m-stefanski/skunk/src/skunk.svg.h

0x3c, 0x73, 0x76, 0x67, 0x20, 0x69, 0x64, 0x3d, 0x22, 0x65, 0x6d, 0x6f, 0x6a, 0x69, 0x22, 0x20, 0x76, 0x69, 0x65, 0x77, 0x42, 0x6f, 0x78, 0x3d, 0x22, 0x30, 0x20, 0x30, 0x20, 0x37, 0x32, 0x20, 0x37, 0x32, 0x22, 0x20, 0x78, 0x6d, 0x6c, 0x6e, 0x73, 0x3d, 0x22, 0x68, 0x74, 0x74, 0x70, 0x3a, 0x2f, 0x2f, 0x77, 0x77, 0x77, 0x2e, 0x77, 0x33, 0x2e, 0x6f, 0x72, 0x67, 0x2f, 0x32, 0x30, 0x30, 0x30, 0x2f, 0x73, 0x76, 0x67, 0x22, 0x3e, 0x0a, 0x20, 0x20, 0x3c, 0x67, 0x20, 0x69, 0x64, 0x3d, 0x22, 0x63, 0x6f, 0x6c, 0x6f, 0x72, 0x22, 0x3e, 0x0a, 0x20, 0x20, 0x20, 0x20, 0x3c, 0x70, 0x61, 0x74, 0x68, 0x20, 0x66, 0x69, 0x6c, 0x6c, 0x3d, 0x22, 0x23, 0x33, 0x66, 0x33, 0x66, 0x33, 0x66, 0x22, 0x20, 0x64, 0x3d, 0x22, 0x4d, 0x32, 0x39, 0x2e, 0x33, 0x36, 0x38, 0x39, 0x2c, 0x35, 0x34, 0x2e, 0x33, 0x39, 0x36, 0x36, 0x6c, 0x2d, 0x31, 0x2e, 0x31, 0x2c, 0x33, 0x2d, 0x33, 0x2c, 0x33, 0x2e, 0x31, 0x68, 0x2d, 0x34, 0x63, 0x2d, 0x31, 0x2e, 0x36, 0x2d, 0x31, 0x2e, 0x32, 0x2c, 0x33, 0x2e, 0x34, 0x2d, 0x33, 0x2e, 0x37, 0x2c, 0x33, 0x2e, 0x34, 0x2d, 0x33, 0x2e, 0x37, 0x76, 0x2d, 0x33, 0x2e, 0x37, 0x6c, 0x2d, 0x2e, 0x32, 0x2d, 0x33, 0x2e, 0x31, 0x41, 0x31, 0x35, 0x2e, 0x38, 0x35, 0x37, 0x34, 0x2c, 0x31, 0x35, 0x2e, 0x38, 0x35, 0x37, 0x34, 0x2c, 0x30, 0x2c, 0x30, 0x2c, 0x31, 0x2c, 0x32, 0x39, 0x2e, 0x33, 0x36, 0x38, 0x39, 0x2c, 0x35, 0x34, 0x2e, 0x33, 0x39, 0x36, 0x36, 0x5a, 0x22, 0x2f, 0x3e, 0x0a, 0x20, 0x20, 0x20, 0x20, 0x3c, 0x70, 0x61, 0x74, 0x68, 0x20, 0x66, 0x69, 0x6c, 0x6c, 0x3d, 0x22, 0x23, 0x33, 0x66, 0x33, 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
