m-stefanski/skunk/src/favicon.png.h

0x89, 0x50, 0x4e, 0x47, 0x0d, 0x0a, 0x1a, 0x0a, 0x00, 0x00, 0x00, 0x0d, 0x49, 0x48, 0x44, 0x52, 0x00, 0x00, 0x00, 0xb4, 0x00, 0x00, 0x00, 0xb4, 0x04, 0x00, 0x00, 0x00, 0x00, 0xdd, 0x56, 0xb4, 0xef, 0x00, 0x00, 0x00, 0x09, 0x70, 0x48, 0x59, 0x73, 0x00, 0x00, 0x24, 0xe8, 0x00, 0x00, 0x24, 0xe8, 0x01, 0x82, 0x63, 0x05, 0x1c, 0x00, 0x00, 0x00, 0x19, 0x74, 0x45, 0x58, 0x74, 0x53, 0x6f, 0x66, 0x74, 0x77, 0x61, 0x72, 0x65, 0x00, 0x77, 0x77, 0x77, 0x2e, 0x69, 0x6e, 0x6b, 0x73, 0x63, 0x61, 0x70, 0x65, 0x2e, 0x6f, 0x72, 0x67, 0x9b, 0xee, 0x3c, 0x1a, 0x00, 0x00, 0x08, 0x27, 0x49, 0x44, 0x41, 0x54, 0x68, 0xde, 0xed, 0x9a, 0x5b, 0x6c, 0x14, 0x65, 0x14, 0x80, 0xcf, 0xee, 0xd2, 0x52, 0x2e, 0xea, 0x42, 0xf1, 0xde, 0xc4, 0x61, 0x57, 0xe5, 0x41, 0x12, 0xa7, 0x9d, 0xa5, 0x08, 0xa2, 0xa2, 0xab, 0x88, 0x8a, 0x72, 0x13, 0x12, 0xb4, 0xda, 0x0a, 0x28, 0xa0, 0x55, 0x49, 0x30, 0x85, 0x60, 0x0d, 0x8d, 0x4a, 0x88, 0xb1, 0x4a, 0x4d, 0x80, 0x44, 0xad, 0x42, 0x42, 0x8c, 0x3e, 0x6c, 0xa0, 0x48, 0xc5, 0x20, 0x9b, 0x60, 0x29, 0xb5, 0xbb, 0x3b, 0x5b, 0x88, 0x09, 0x0f, 0x3e, 0x90, 0x34, 0x31, 0xe8, 0x8b, 0x0d, 0x7d, 0x10, 0xe5, 0xda, 0x8e, 0xff, 0x65, 0xee, 0xff, 0xdf, 0xd9, 0xb9, 0x11, 0x5f, 0xf6, 0xbc, 0xec, 0xee, 0xb4, 0xfb, 0xcd, 0xd9, 0x73, 0xce, 0x7f, 0xce, 0x7f, 0xce, 0x3f, 0x50, 0xbc, 0x6e, 0x02, 0x65, 0x74, 0x19, 0x5d, 0x46, 0x97, 0xd1, 0x65, 0x74, 0x19, 0x5d, 0x46, 0x97, 0xd1, 0xd7, 0x0b, 0x7d, 0xb4, 0x65, 0xc5, 0xca, 0x2d, 0xd9, 0xeb, 0x80, 0xce, 0x3d, 0x0a, 0x44, 0x66, 0x67, 0xc3, 0x46, 0x7f, 0x03, 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
