m-stefanski/skunk/src/style.css.h

0x62, 0x6f, 0x64, 0x79, 0x20, 0x7b, 0x0a, 0x20, 0x20, 0x66, 0x6f, 0x6e, 0x74, 0x2d, 0x66, 0x61, 0x6d, 0x69, 0x6c, 0x79, 0x3a, 0x20, 0x73, 0x61, 0x6e, 0x73, 0x2d, 0x73, 0x65, 0x72, 0x69, 0x66, 0x3b, 0x0a, 0x20, 0x20, 0x63, 0x6f, 0x6c, 0x6f, 0x72, 0x3a, 0x20, 0x23, 0x30, 0x30, 0x30, 0x30, 0x30, 0x30, 0x3b, 0x0a, 0x20, 0x20, 0x62, 0x61, 0x63, 0x6b, 0x67, 0x72, 0x6f, 0x75, 0x6e, 0x64, 0x2d, 0x63, 0x6f, 0x6c, 0x6f, 0x72, 0x3a, 0x20, 0x23, 0x66, 0x66, 0x66, 0x66, 0x66, 0x66, 0x3b, 0x0a, 0x7d, 0x0a, 0x0a, 0x2e, 0x68, 0x65, 0x61, 0x64, 0x65, 0x72, 0x20, 0x7b, 0x0a, 0x20, 0x20, 0x74, 0x65, 0x78, 0x74, 0x2d, 0x61, 0x6c, 0x69, 0x67, 0x6e, 0x3a, 0x20, 0x63, 0x65, 0x6e, 0x74, 0x65, 0x72, 0x3b, 0x0a, 0x7d, 0x0a, 0x0a, 0x2e, 0x68, 0x65, 0x61, 0x64, 0x65, 0x72, 0x20, 0x68, 0x31, 0x2c, 0x20, 0x69, 0x6d, 0x67, 0x20, 0x7b, 0x0a, 0x20, 0x20, 0x64, 0x69, 0x73, 0x70, 0x6c, 0x61, 0x79, 0x3a, 0x20, 0x69, 0x6e, 0x6c, 0x69, 0x6e, 0x65, 0x3b, 0x0a, 0x7d, 0x0a, 0x0a, 0x2e, 0x68, 0x65, 0x61, 0x64, 0x65, 0x72, 0x20, 0x68, 0x31, 0x20, 0x7b, 0x0a, 0x20, 0x20, 0x76, 0x65, 0x72, 0x74, 0x69, 0x63, 0x61, 0x6c, 0x2d, 0x61, 0x6c, 0x69, 0x67, 0x6e, 0x3a, 0x20, 0x6d, 0x69, 0x64, 0x64, 0x6c, 0x65, 0x3b, 0x0a, 0x20, 0x20, 0x6d, 0x61, 0x72, 0x67, 0x69, 0x6e, 0x2d, 0x6c, 0x65, 0x66, 0x74, 0x3a, 0x20, 0x2d, 0x30, 0x2e, 0x34, 0x65, 0x6d, 0x3b, 0x0a, 0x7d, 0x0a, 0x0a, 0x2e, 0x68, 0x65, 0x61, 0x64, 0x65, 0x72, 0x20, 0x69, 0x6d, 0x67, 0x20, 0x7b, 0x0a, 0x20, 0x20, 0x68, 0x65, 0x69, 0x67, 0x68, 0x74, 0x3a, 0x20, 0x34, 0x65, 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
