m-stefanski/skunk/src/cache.manifest.h

0x43, 0x41, 0x43, 0x48, 0x45, 0x20, 0x4d, 0x41, 0x4e, 0x49, 0x46, 0x45, 0x53, 0x54, 0x0a, 0x0a, 0x23, 0x20, 0x56, 0x65, 0x72, 0x73, 0x69, 0x6f, 0x6e, 0x20, 0x31, 0x2e, 0x30, 0x0a, 0x0a, 0x4e, 0x45, 0x54, 0x57, 0x4f, 0x52, 0x4b, 0x3a, 0x0a, 0x2a, 0x0a, 0x0a, 0x43, 0x41, 0x43, 0x48, 0x45, 0x3a, 0x0a, 0x69, 0x6e, 0x64, 0x65, 0x78, 0x2e, 0x68, 0x74, 0x6d, 0x6c, 0x0a, 0x66, 0x61, 0x76, 0x69, 0x63, 0x6f, 0x6e, 0x2e, 0x70, 0x6e, 0x67, 0x0a, 0x73, 0x6b, 0x75, 0x6e, 0x6b, 0x2e, 0x73, 0x76, 0x67, 0x0a, 0x73, 0x74, 0x79, 0x6c, 0x65, 0x2e, 0x63, 0x73, 0x73, 0x0a, 0x0a, 0x46, 0x41, 0x4c, 0x4c, 0x42, 0x41, 0x43, 0x4b, 0x3a, 
